MacGyverr/Westinghouse-Spotify-Clock/images/20221014_142344.jpg

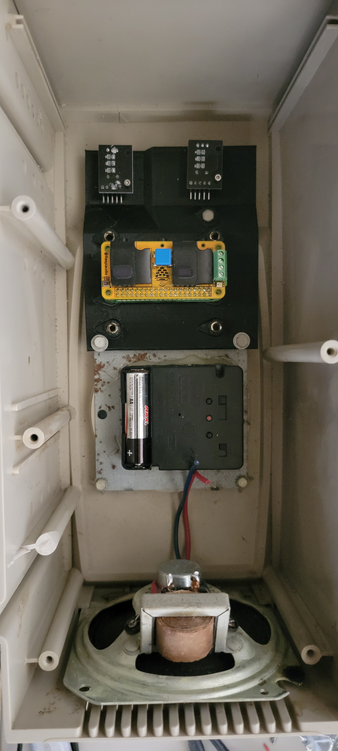
images/20221014_142344.jpg
