MacGyverr/Westinghouse-Spotify-Clock/images/20221029_140240.jpg

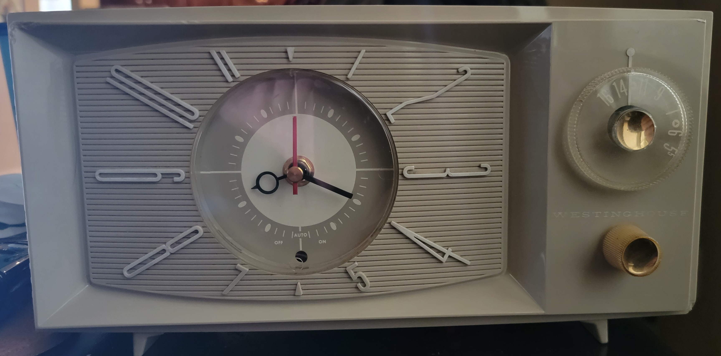
images/20221029_140240.jpg
