MacGyverr/Westinghouse-Spotify-Clock/images/20221029_151903.jpg

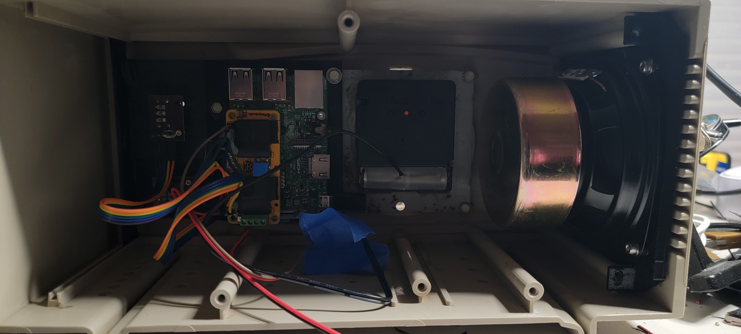
images/20221029_151903.jpg
