MacGyverr/Westinghouse-Spotify-Clock/images/20221029_151911.jpg

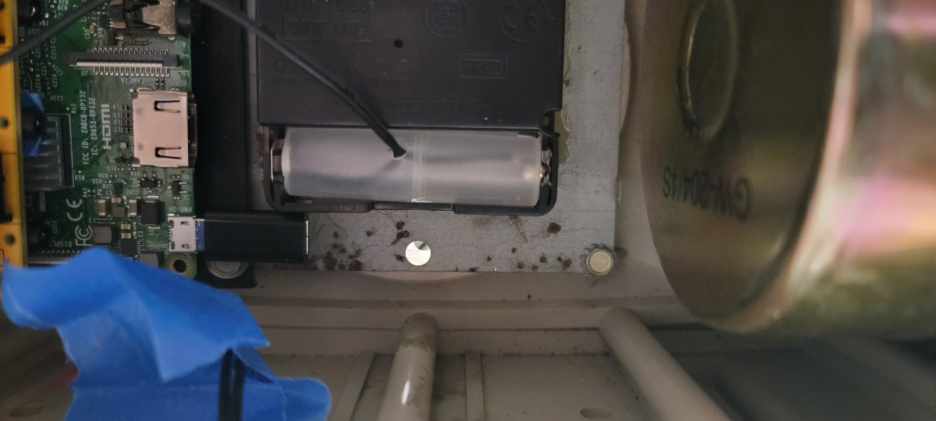
images/20221029_151911.jpg
