MacGyverr/Westinghouse-Spotify-Clock/images/20221104_140253.jpg

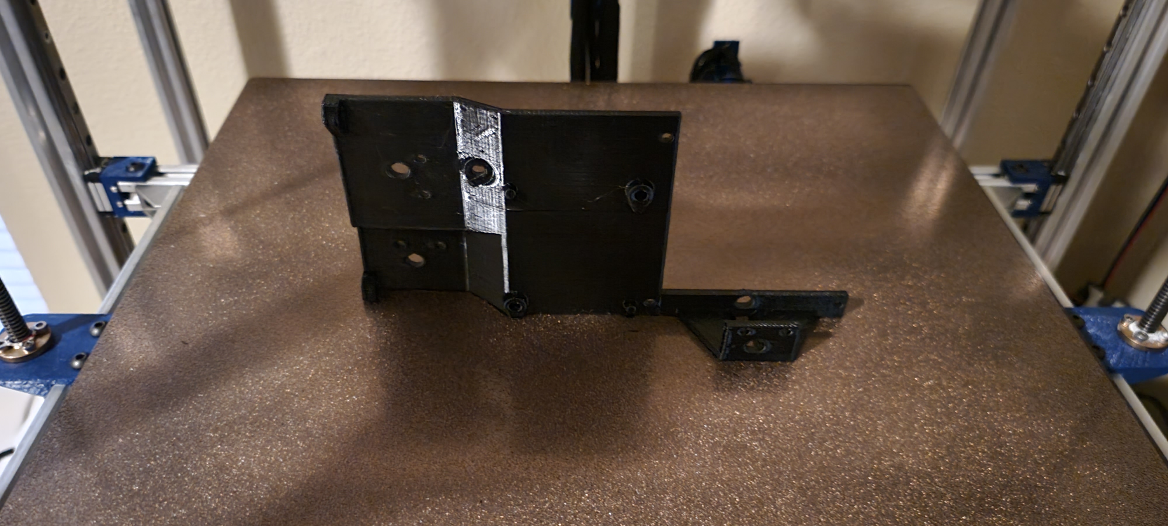
images/20221104_140253.jpg
