MacGyverr/Westinghouse-Spotify-Clock/images/20221104_140519.jpg

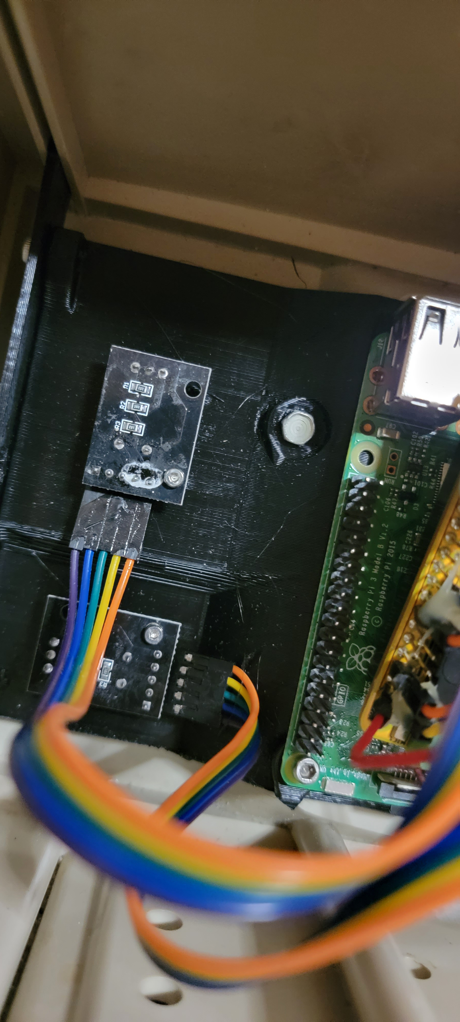
images/20221104_140519.jpg
