MacGyverr/Westinghouse-Spotify-Clock/images/20221104_140754.jpg

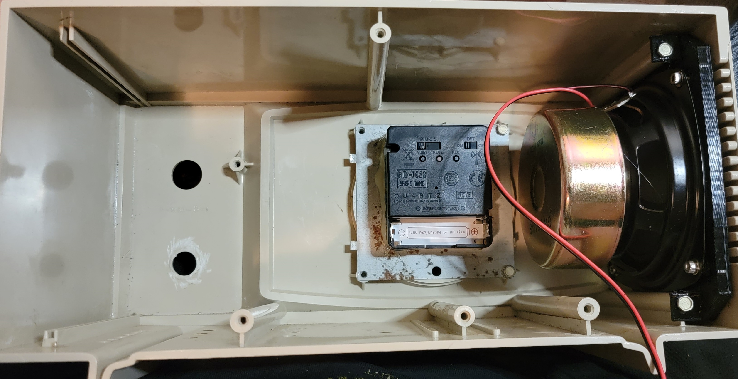
images/20221104_140754.jpg
