MacGyverr/Westinghouse-Spotify-Clock/images/20221104_140803.jpg

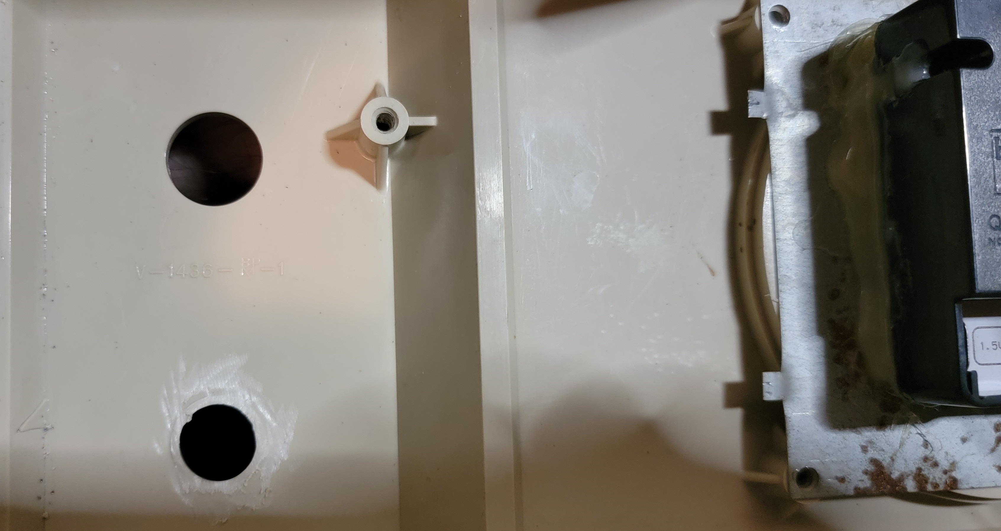
images/20221104_140803.jpg
