MacGyverr/Westinghouse-Spotify-Clock/images/20221104_141330.jpg

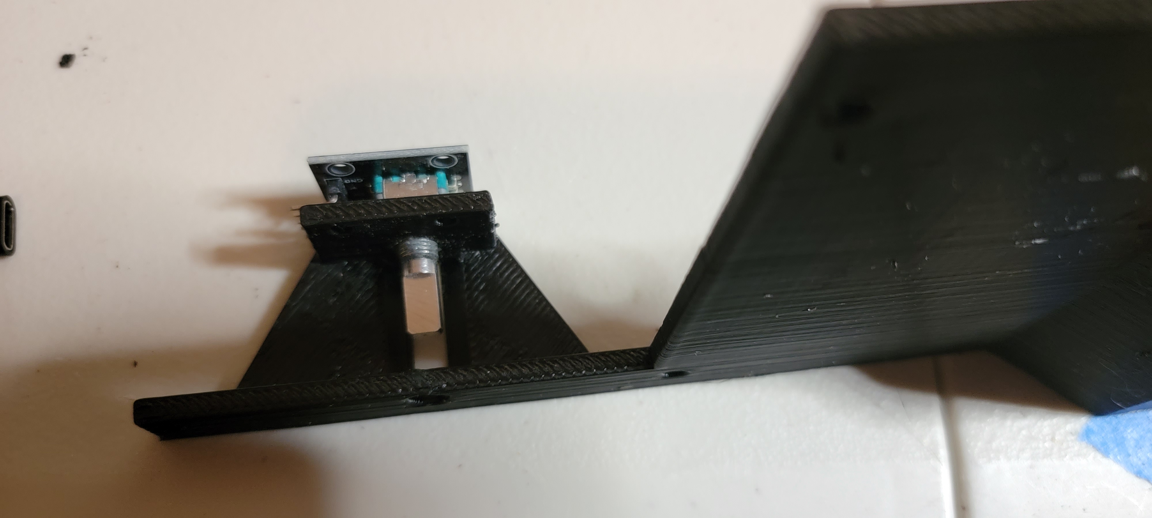
images/20221104_141330.jpg
