MacGyverr/Westinghouse-Spotify-Clock/images/20221104_172836.jpg

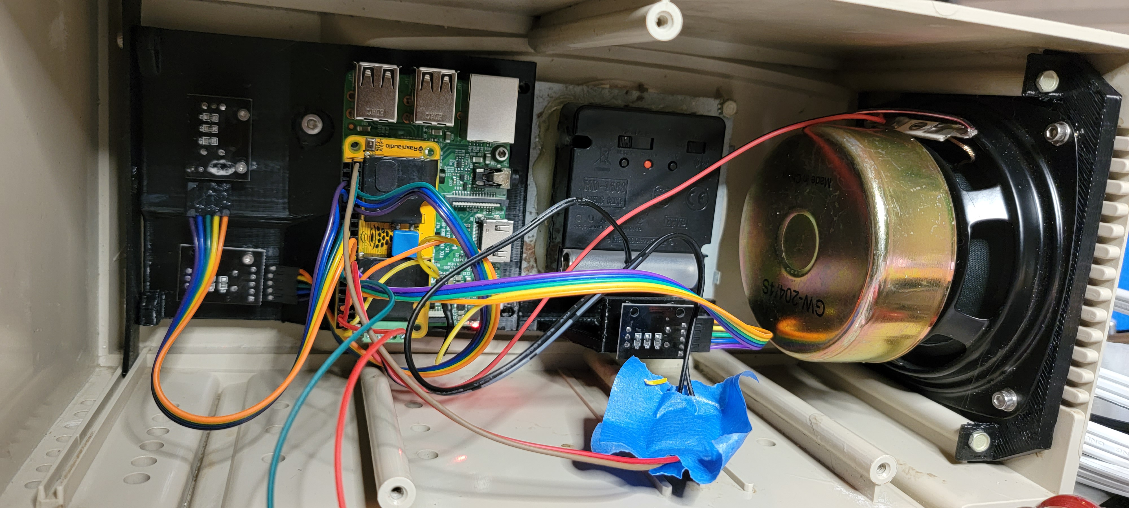
images/20221104_172836.jpg
