MacGyverr/Westinghouse-Spotify-Clock/images/20221104_172841.jpg

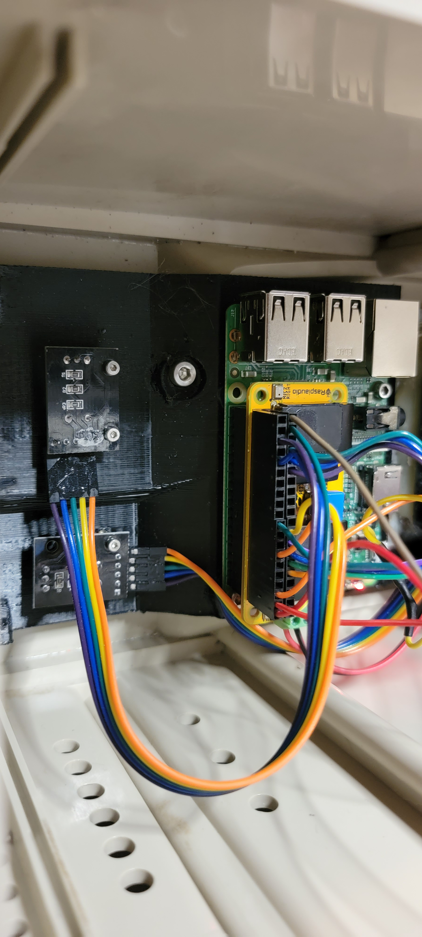
images/20221104_172841.jpg
