MacGyverr/Westinghouse-Spotify-Clock/images/20221104_172847.jpg

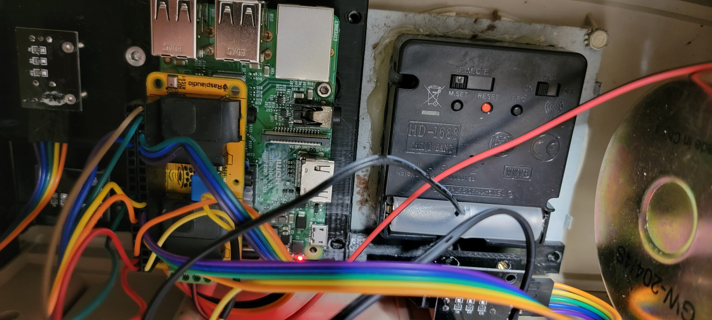
images/20221104_172847.jpg
