MacGyverr/Westinghouse-Spotify-Clock/images/20221104_172852.jpg

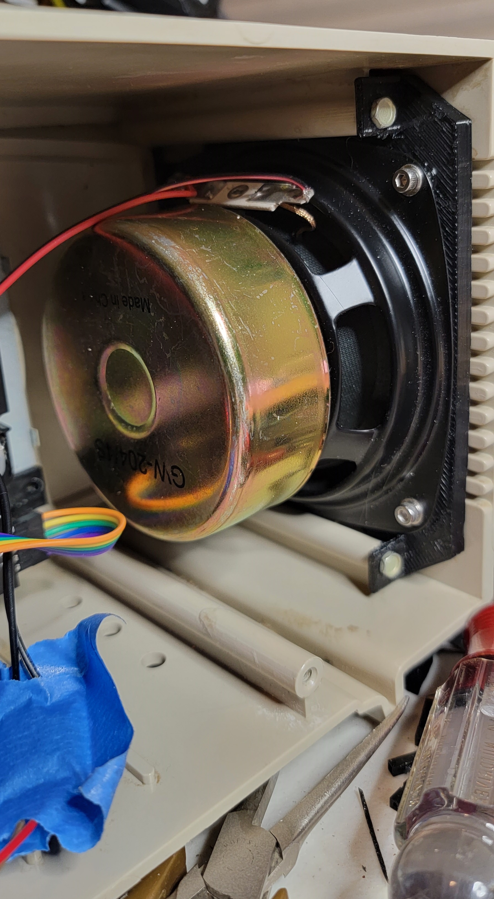
images/20221104_172852.jpg
