MacGyverr/Westinghouse-Spotify-Clock/images/20221105_144720.jpg

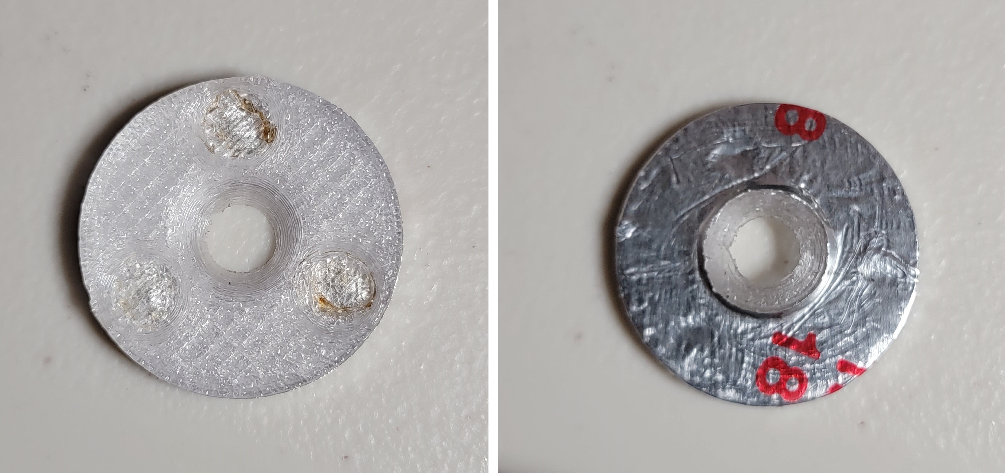
images/20221105_144720.jpg
