MacGyverr/Westinghouse-Spotify-Clock/images/20221105_152253.jpg

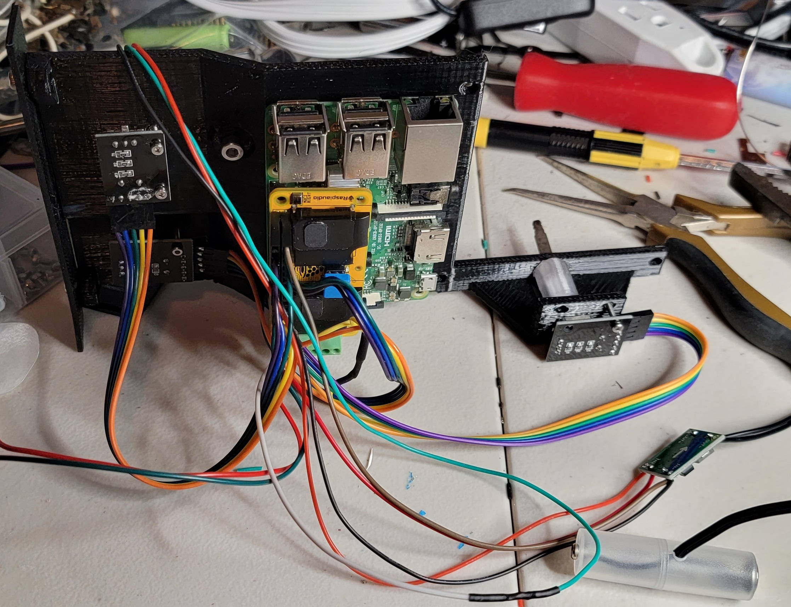
images/20221105_152253.jpg
