MacGyverr/Westinghouse-Spotify-Clock/images/20221105_152256.jpg

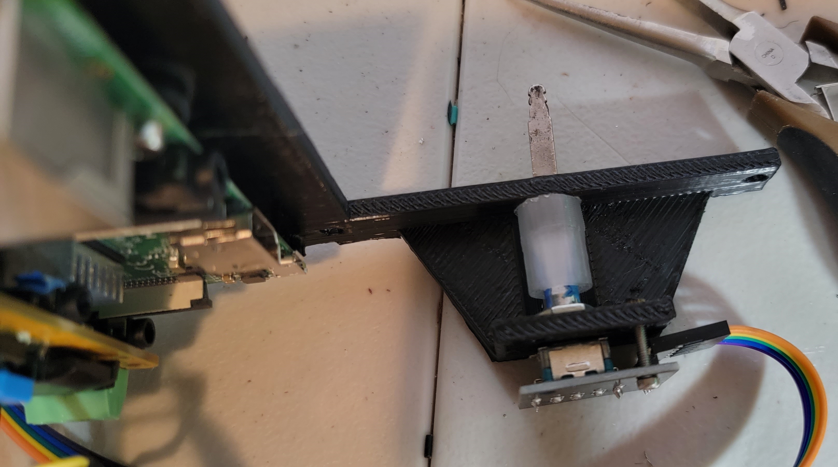
images/20221105_152256.jpg
