MacGyverr/Westinghouse-Spotify-Clock/images/20221105_152304.jpg

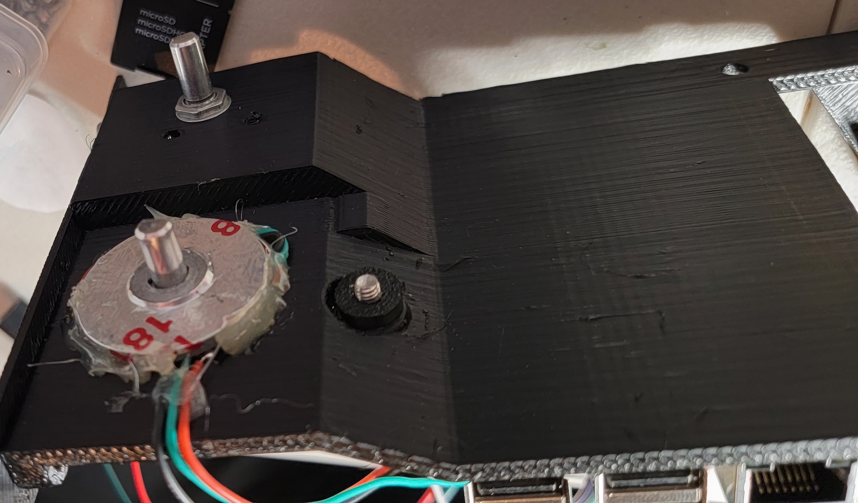
images/20221105_152304.jpg
