MacGyverr/Westinghouse-Spotify-Clock/STLs/replacement-face.stl

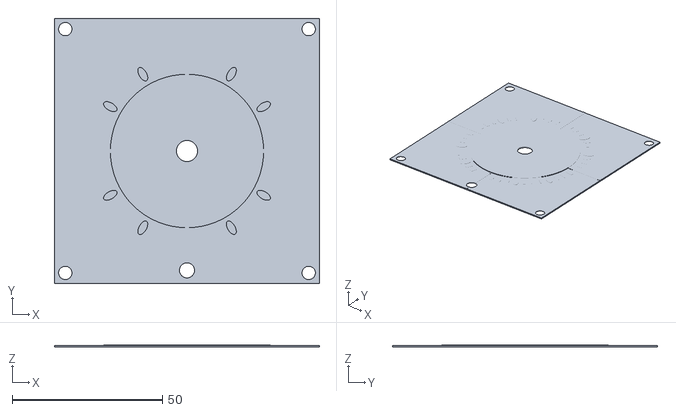
[picture p39: CAD file, 2024-01-01]
STLs/replacement-face.stl
88.2 x 88.3 x 0.719
