MacGyverr/Westinghouse-Spotify-Clock/STLs/mounting-plate-support.stl

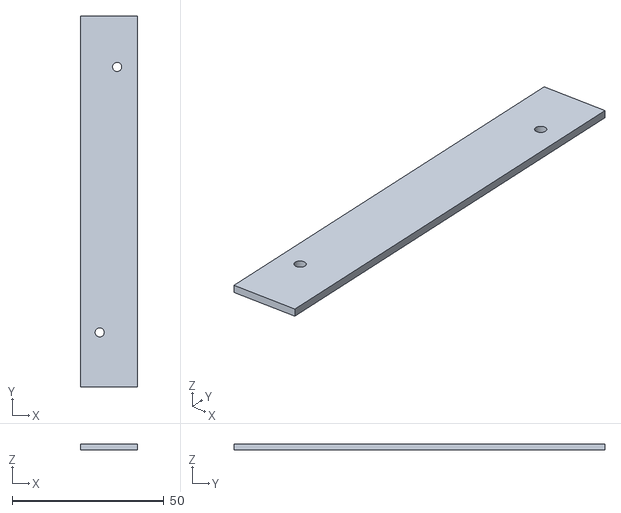
[picture p40: CAD file, 2024-01-01]
STLs/mounting-plate-support.stl
18.7 x 122.3 x 2.00
